hieu-hm/wood-resin-keycap-cnc-3020/drawings/keycap_1u_r1_sample_exact_square_recess_bottom.png

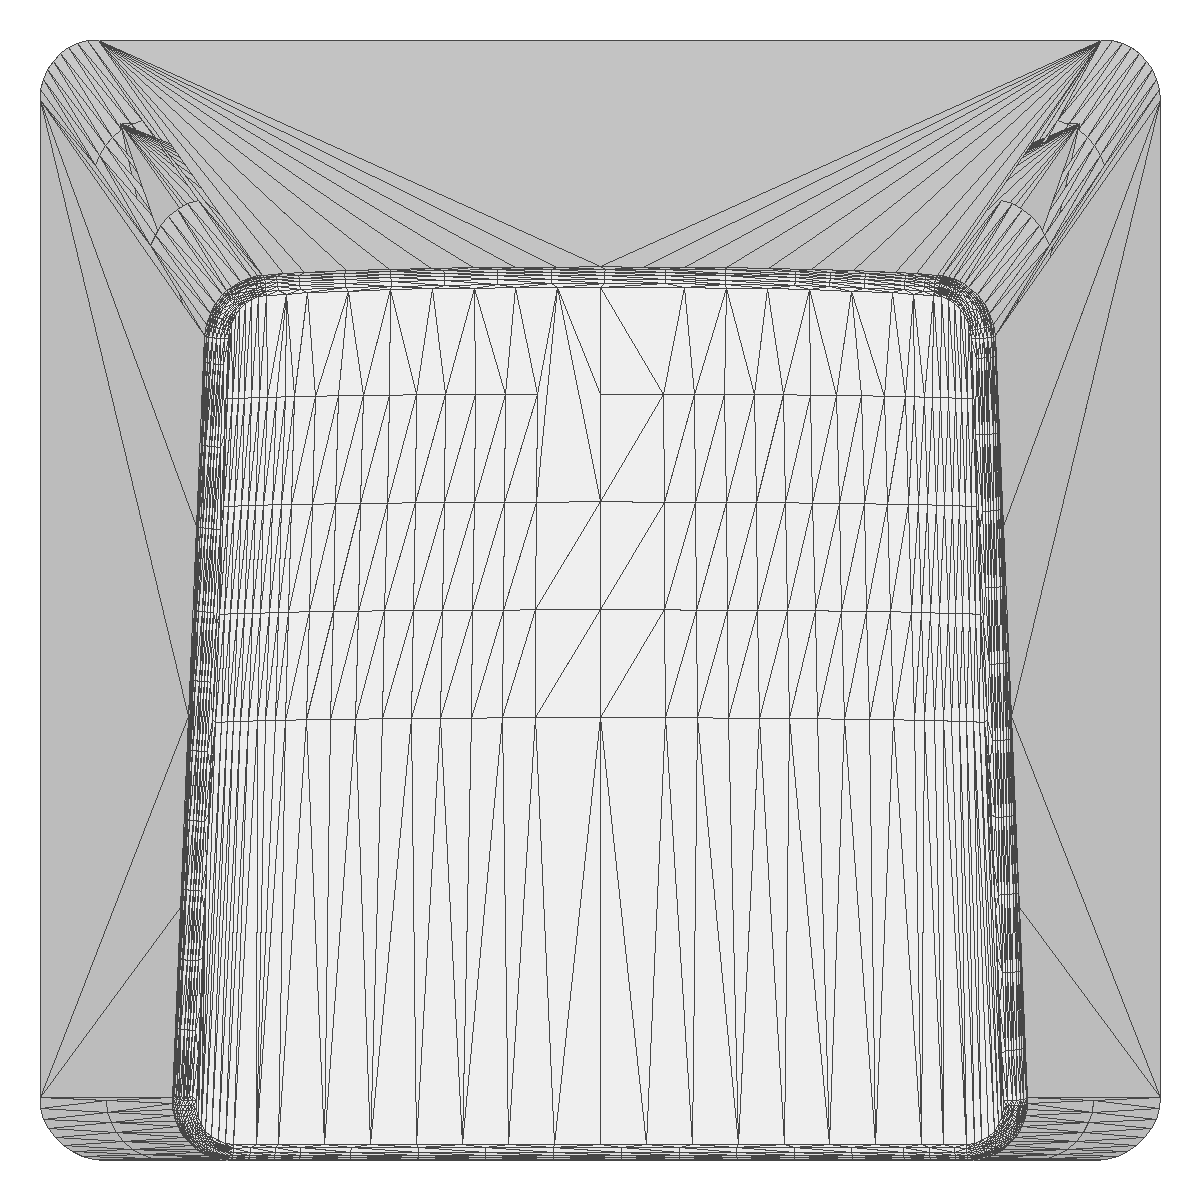
drawings/keycap_1u_r1_sample_exact_square_recess_bottom.png
